tharejarehan0-a11y/Fleeboard/Media/card.png

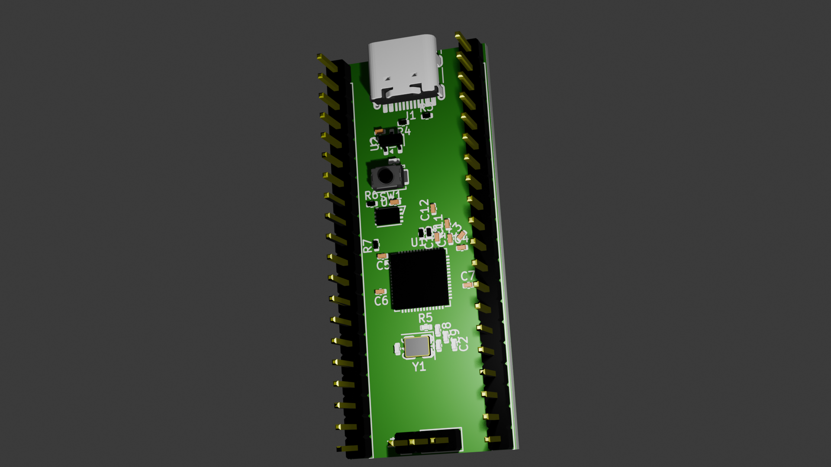
Media/card.png
